GDSC-HSU/gateway-devices/ESP32-BLE/src/MyBLE.cpp

#include "MyBLE.h"
// TODO Setup for other services
MyBLE::MyBLE() {}

void MyBLE::init(NimBLEServer *pBLE_SERVER)
{
    gpServer = pBLE_SERVER;
    gpServer->setCallbacks(new MyBLEServerCallbacks());
    // gpServer->start()

    // Bringing ours BLE Services up and it corrsponding charecteristic
    proximityBLE();
    thermometerBLE();
    radarBLE();
    rfidBLE();

    /// Advertisting GATT
    const char *manufacturer = "GDSC-HSU:v0.1.2";
    NimBLEAdvertising *pAdvertising = NimBLEDevice::getAdvertising();
    // pAdvertising->addServiceUUID(BLE_SERVICE_PROXIMITY_UUID);
    pAdvertising->setManufacturerData(manufacturer);

    pAdvertising->addServiceUUID(BLE_SERVICE_PROXIMITY_UUID);
    pAdvertising->addServiceUUID(BLE_SERVICE_THERMOMETER_UUID);
    pAdvertising->addServiceUUID(BLE_SERVICE_RADAR_UUID);
    pAdvertising->addServiceUUID(BLE_SERVICE_RFID_UUID);
    pAdvertising->addServiceUUID(BLE_SERVICE_BATTERY);
    pAdvertising->addServiceUUID(BLE_SERVICE_OTA_UUID);

    pAdvertising->start();
    ////
}

void MyBLE::proximityBLE()
{
    pProximityServices = gpServer->createService(BLE_SERVICE_PROXIMITY_UUID);
    pProximityServices->createCharacteristic(BLE_CHARACTERISTIC_PROXIMITY_DISTANCE, NIMBLE_PROPERTY::READ | NIMBLE_PROPERTY::NOTIFY);
    pProximityServices->start();
}

void MyBLE::thermometerBLE()
{
    pThermometerServices = gpServer->createService(BLE_SERVICE_THERMOMETER_UUID);
    pThermometerServices->createCharacteristic(BLE_CHARACTERISTIC_THERMOMETER_READ, NIMBLE_PROPERTY::READ | NIMBLE_PROPERTY::NOTIFY);
    pThermometerServices->start();
}

void MyBLE::radarBLE()
{
    pRadarServices = gpServer->createService(BLE_SERVICE_RADAR_UUID);
    pRadarServices->createCharacteristic(BLE_CHARACTERISTIC_RADAR_UUID, NIMBLE_PROPERTY::READ | NIMBLE_PROPERTY::NOTIFY);
    pRadarServices->start();
}

void MyBLE::otaBLE()
{
    pOTAServices = gpServer->createService(BLE_SERVICE_OTA_UUID);
    // BLE_CHARACTERISTIC_OTA_CONTROL to acknowledgment current version checking
    pOTAServices->createCharacteristic(BLE_CHARACTERISTIC_OTA_CONTROL, NIMBLE_PROPERTY::READ | NIMBLE_PROPERTY::NOTIFY);

    pOTAServices->createCharacteristic(BLE_CHARACTERISTIC_OTA_WRITE_NO_RSP, NIMBLE_PROPERTY::WRITE_NR);
}

void MyBLE::rfidBLE()
{
    pRFIDServices = gpServer->createService(BLE_SERVICE_RFID_UUID);
    pRFIDServices->createCharacteristic(BLE_CHARACTERISTIC_RFID_READ, NIMBLE_PROPERTY::READ | NIMBLE_PROPERTY::NOTIFY);
    pRFIDServices->start();
}

/// ------------------ SET BLE DATA AND NOTIFY TO MOBILE APP
void MyBLE::setProximity(String number, bool isNotify)
{
    NimBLECharacteristic *pCharacteristic = pProximityServices->getCharacteristic(BLE_CHARACTERISTIC_PROXIMITY_DISTANCE);
    pCharacteristic->setValue(std::string(number.c_str()));
    if (isNotify)
    {
        pCharacteristic->notify();
    }
}
void MyBLE::setThermometer(String number, bool isNotify)
{
    NimBLECharacteristic *pCharacteristic = pThermometerServices->getCharacteristic(BLE_CHARACTERISTIC_THERMOMETER_READ);
    pCharacteristic->setValue(std::string(number.c_str()));
    if (isNotify)
    {
        pCharacteristic->notify();
    }
}

void MyBLE::setRadar(String number, bool isNotify)
{
    NimBLECharacteristic *pCharacteristic = pRadarServices->getCharacteristic(BLE_CHARACTERISTIC_RADAR_UUID);
    pCharacteristic->setValue(std::string(number.c_str()));
    if (isNotify)
    {
        pCharacteristic->notify();
    }
}

void MyBLE::setRFID(String number, bool isNotify)
{
    NimBLECharacteristic *pCharacteristic = pRFIDServices->getCharacteristic(BLE_CHARACTERISTIC_RFID_READ);
    pCharacteristic->setValue(std::string(number.c_str()));
    if (isNotify)
    {
        pCharacteristic->notify();
    }
}
bool MyBLE::isMobileConnected(){
   return deviceConnected;
}
