GDSC-HSU/gateway-devices/ESP32-BLE/src/BLE_DESIGN.g.h

// THIS IS GENERATED IN ble_uuid_conf.yml
#ifndef DEVICE_NAME
#define DEVICE_NAME "esp32-gateway"
#endif
#ifndef BLE_SERVICE_PROXIMITY_UUID
#define BLE_SERVICE_PROXIMITY_UUID "00000A00-5226-4AE0-8977-656FD3C42DA2"
#endif

#ifndef BLE_CHARACTERISTIC_PROXIMITY_DISTANCE
#define BLE_CHARACTERISTIC_PROXIMITY_DISTANCE "00000A02-5226-4AE0-8977-656FD3C42DA2"
#endif

#ifndef BLE_SERVICE_THERMOMETER_UUID
#define BLE_SERVICE_THERMOMETER_UUID "00000B00-5226-4AE0-8977-656FD3C42DA2"
#endif

#ifndef BLE_CHARACTERISTIC_THERMOMETER_READ
#define BLE_CHARACTERISTIC_THERMOMETER_READ "00000B01-5226-4AE0-8977-656FD3C42DA2"
#endif

#ifndef BLE_SERVICE_RFID_UUID
#define BLE_SERVICE_RFID_UUID "00000D00-5226-4AE0-8977-656FD3C42DA2"
#endif

#ifndef BLE_CHARACTERISTIC_RFID_READ
#define BLE_CHARACTERISTIC_RFID_READ "00000D01-5226-4AE0-8977-656FD3C42DA2"
#endif

#ifndef BLE_SERVICE_RADAR_UUID
#define BLE_SERVICE_RADAR_UUID "00000C00-5226-4AE0-8977-656FD3C42DA2"
#endif

#ifndef BLE_CHARACTERISTIC_RADAR_UUID
#define BLE_CHARACTERISTIC_RADAR_UUID "00000C01-5226-4AE0-8977-656FD3C42DA2"
#endif

#ifndef BLE_SERVICE_OTA_UUID
#define BLE_SERVICE_OTA_UUID "1d14d6ee-fd63-4fa1-bfa4-8f47b42119f0"
#endif

#ifndef BLE_CHARACTERISTIC_OTA_CONTROL
#define BLE_CHARACTERISTIC_OTA_CONTROL "f7bf3564-fb6d-4e53-88a4-5e37e0326063"
#endif

#ifndef BLE_CHARACTERISTIC_OTA_WRITE_NO_RSP
#define BLE_CHARACTERISTIC_OTA_WRITE_NO_RSP "e984227f3-34fc-4045-a5d0-2c581f81a153"
#endif

#ifndef BLE_SERVICE_BATTERY
#define BLE_SERVICE_BATTERY "180F"
#endif

#ifndef BLE_CHARACTERISTIC_BATTERY_LEVEL
#define BLE_CHARACTERISTIC_BATTERY_LEVEL "2A19"
#endif
